alexcustos/wrn-project/wrn/main.h

// Copyright (c) 2016 Aleksandr Borisenko
// Distributed under the terms of the GNU General Public License v2

#ifndef MAIN_H_
#define MAIN_H_

#ifdef DEBUG
#define IF_DEBUG(x) ({x;})
#else
#define IF_DEBUG(x)
#endif

#endif /* MAIN_H_ */
